Arakon/ESP32-Nightscout-TFT-Graph/DoubleDown.h

#define DOUBLEDOWN_HEIGHT 50
#define DOUBLEDOWN_WIDTH 50

// array size is 5000
static const uint16_t DoubleDown[] PROGMEM  = {
  0x0000, 0x0000, 0x0000, 0x0000, 0x0000, 0x0000, 0x5820, 0xa061, 0xc061, 0xb842, 0xb841, 0xb861, 0xb861, 0xb841, 0xc061, 0xd061, 0xc062, 0xa021, 0x3800, 0x0000, 0x0000, 0x0000, 0x0000, 0x0000, 0x0000, 0x0000, 0x0000, 0x0000, 0x0000, 0x0000, 0x0000, 0x4820, 0xb841, 0xb061, 0xb861, 0xb841, 0xb841, 0xb841, 0xb861, 0xb841, 0xc061, 0xe062, 0xb841, 0x3800, 0x0000, 0x0000, 0x0000, 0x0000, 0x0000, 0x0000, 
  0x0000, 0x0000, 0x0000, 0x0000, 0x0000, 0x0000, 0x6020, 0xb041, 0xd061, 0xc041, 0xc041, 0xc841, 0xc041, 0xc061, 0xd841, 0xf040, 0xe040, 0xa841, 0x3000, 0x0000, 0x0000, 0x0000, 0x0000, 0x0000, 0x0000, 0x0000, 0x0000, 0x0000, 0x0000, 0x0000, 0x0000, 0x5020, 0xc041, 0xc041, 0xc841, 0xc841, 0xc061, 0xc040, 0xc861, 0xd041, 0xe041, 0xf840, 0xc861, 0x3820, 0x0000, 0x0000, 0x0000, 0x0000, 0x0000, 0x0000, 
  0x0000, 0x0000, 0x0000, 0x0000, 0x0000, 0x0000, 0x6020, 0xb041, 0xd841, 0xc840, 0xd060, 0xd041, 0xd061, 0xd061, 0xe841, 0xf840, 0xf020, 0xa820, 0x3000, 0x0000, 0x0000, 0x0000, 0x0000, 0x0000, 0x0000, 0x0000, 0x0000, 0x0000, 0x0000, 0x0000, 0x0000, 0x5020, 0xc860, 0xc840, 0xd041, 0xd041, 0xc861, 0xc860, 0xd061, 0xe061, 0xf041, 0xf860, 0xd041, 0x3820, 0x0000, 0x0000, 0x0000, 0x0000, 0x0000, 0x0000, 
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
};
