Arakon/ESP32-Nightscout-TFT-Graph/Down.h

#define DOWN_HEIGHT 50
#define DOWN_WIDTH 50

// array size is 5000
static const uint16_t Down[] PROGMEM  = {
  0x0000, 0x0000, 0x0000, 0x0000, 0x0000, 0x0000, 0x0000, 0x0000, 0x0000, 0x0000, 0x0000, 0x0000, 0x0000, 0x0000, 0x0000, 0x0000, 0x0000, 0x2b02, 0x4d24, 0x5564, 0x5564, 0x5564, 0x5564, 0x5585, 0x5584, 0x5565, 0x5564, 0x5585, 0x5d87, 0x6da8, 0x65e7, 0x6587, 0x3b64, 0x0000, 0x0000, 0x0000, 0x0000, 0x0000, 0x0000, 0x0000, 0x0000, 0x0000, 0x0000, 0x0000, 0x0000, 0x0000, 0x0000, 0x0000, 0x0000, 0x0000, 
  0x0000, 0x0000, 0x0000, 0x0000, 0x0000, 0x0000, 0x0000, 0x0000, 0x0000, 0x0000, 0x0000, 0x0000, 0x0000, 0x0000, 0x0000, 0x0000, 0x0000, 0x2ae3, 0x4d25, 0x5da6, 0x5d86, 0x5d86, 0x6587, 0x6586, 0x5da7, 0x5d86, 0x5d86, 0x65a8, 0x75eb, 0x860c, 0x8e6d, 0x75ca, 0x3343, 0x0000, 0x0000, 0x0000, 0x0000, 0x0000, 0x0000, 0x0000, 0x0000, 0x0000, 0x0000, 0x0000, 0x0000, 0x0000, 0x0000, 0x0000, 0x0000, 0x0000, 
  0x0000, 0x0000, 0x0000, 0x0000, 0x0000, 0x0000, 0x0000, 0x0000, 0x0000, 0x0000, 0x0000, 0x0000, 0x0000, 0x0000, 0x0000, 0x0000, 0x0000, 0x2ae2, 0x5545, 0x65c8, 0x65a7, 0x65a8, 0x65a8, 0x65a7, 0x65a8, 0x65a7, 0x65a8, 0x75ea, 0x862d, 0x964f, 0xa6b1, 0x7deb, 0x3343, 0x0000, 0x0000, 0x0000, 0x0000, 0x0000, 0x0000, 0x0000, 0x0000, 0x0000, 0x0000, 0x0000, 0x0000, 0x0000, 0x0000, 0x0000, 0x0000, 0x0000, 
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
};
